Shubhroto-M/Vanguard-25-BMS/Screenshot 2026-04-05 005655.png

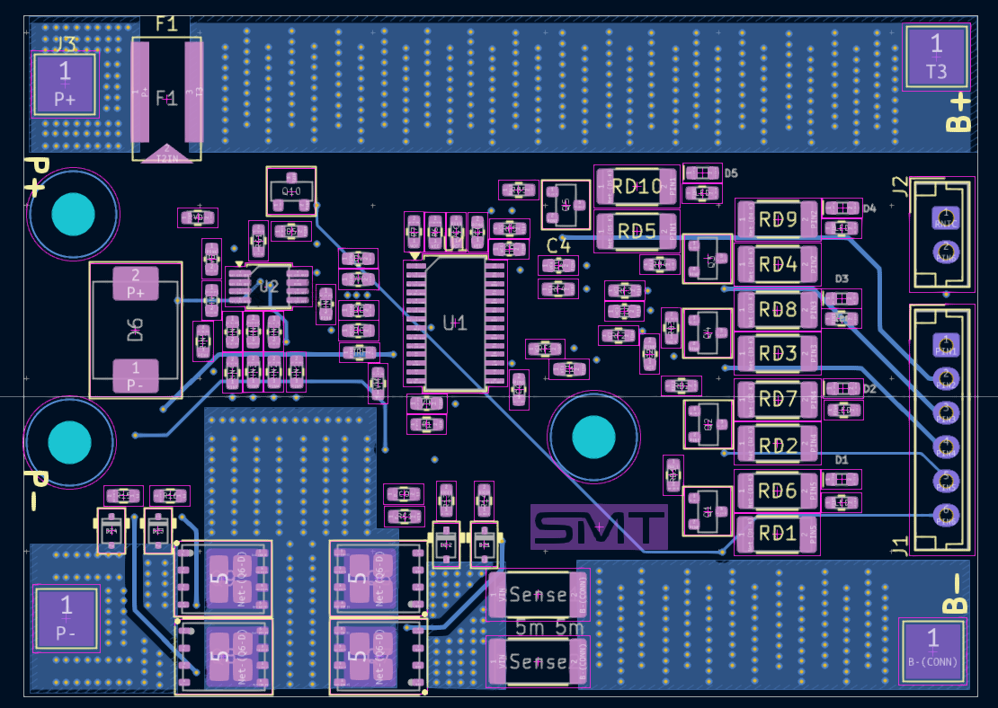
Screenshot 2026-04-05 005655.png
